ZIOCC/Zio-Qwiic-Ultrasonic-Distance-Sensor/STM8 Gateway Firmware/STM8L15x_StdPeriph_Driver/inc/stm8l15x_rtc.h

/**
  ******************************************************************************
  * @file    stm8l15x_rtc.h
  * @author  MCD Application Team
  * @version V1.5.0
  * @date    13-May-2011
  * @brief   This file contains all the functions prototypes for the RTC 
  *          firmware library.
  ******************************************************************************
  * @attention
  *
  * THE PRESENT FIRMWARE WHICH IS FOR GUIDANCE ONLY AIMS AT PROVIDING CUSTOMERS
  * WITH CODING INFORMATION REGARDING THEIR PRODUCTS IN ORDER FOR THEM TO SAVE
  * TIME. AS A RESULT, STMICROELECTRONICS SHALL NOT BE HELD LIABLE FOR ANY
  * DIRECT, INDIRECT OR CONSEQUENTIAL DAMAGES WITH RESPECT TO ANY CLAIMS ARISING
  * FROM THE CONTENT OF SUCH FIRMWARE AND/OR THE USE MADE BY CUSTOMERS OF THE
  * CODING INFORMATION CONTAINED HEREIN IN CONNECTION WITH THEIR PRODUCTS.
  *
  * <h2><center>&copy; COPYRIGHT 2011 STMicroelectronics</center></h2>
  ******************************************************************************  
  */
/* Define to prevent recursive inclusion -------------------------------------*/
#ifndef __STM8L15x_RTC_H
#define __STM8L15x_RTC_H

/* Includes ------------------------------------------------------------------*/
#include "stm8l15x.h"

/** @addtogroup STM8L15x_StdPeriph_Driver
  * @{
  */

/** @addtogroup RTC
  * @{
  */ 
  
/* Exported types ------------------------------------------------------------*/
/** @defgroup RTC_Exported_Types
  * @{
  */

/** @defgroup RTC_Weekdays
  * @{
  */ 
typedef enum
{
  RTC_Weekday_Monday      =  ((uint8_t)0x01), /*!< WeekDay is Monday */
  RTC_Weekday_Tuesday     =  ((uint8_t)0x02), /*!< WeekDay is Tuesday */
  RTC_Weekday_Wednesday   =  ((uint8_t)0x03), /*!< WeekDay is Wednesday */
  RTC_Weekday_Thursday    =  ((uint8_t)0x04), /*!< WeekDay is Thursday */
  RTC_Weekday_Friday      =  ((uint8_t)0x05), /*!< WeekDay is Friday */
  RTC_Weekday_Saturday    =  ((uint8_t)0x06), /*!< WeekDay is Saturday */
  RTC_Weekday_Sunday      =  ((uint8_t)0x07)  /*!< WeekDay is Sunday */
}
RTC_Weekday_TypeDef;

/**
  * @}
  */
  
/** @defgroup RTC_Months
  * @{
  */ 
typedef enum
{
  RTC_Month_January   =  ((uint8_t)0x01), /*!< Month is January */
  RTC_Month_February  =  ((uint8_t)0x02), /*!< Month is February */
  RTC_Month_March     =  ((uint8_t)0x03), /*!< Month is March */
  RTC_Month_April     =  ((uint8_t)0x04), /*!< Month is April */
  RTC_Month_May       =  ((uint8_t)0x05), /*!< Month is May */
  RTC_Month_June      =  ((uint8_t)0x06), /*!< Month is June */
  RTC_Month_July      =  ((uint8_t)0x07), /*!< Month is July */
  RTC_Month_August    =  ((uint8_t)0x08), /*!< Month is August */
  RTC_Month_September =  ((uint8_t)0x09), /*!< Month is September */
  RTC_Month_October   =  ((uint8_t)0x10), /*!< Month is October */
  RTC_Month_November  =  ((uint8_t)0x11), /*!< Month is November */
  RTC_Month_December  =  ((uint8_t)0x12)  /*!< Month is December */
}
RTC_Month_TypeDef;

/**
  * @}
  */
  
/** @defgroup RTC_Hour_Format
  * @{
  */ 
typedef enum
{
  RTC_HourFormat_24  = ((uint8_t)0x00), /*!< Hour Format is 24H */
  RTC_HourFormat_12  = ((uint8_t)0x40)  /*!< Hour Format is 12H (using AM/PM) */
}
RTC_HourFormat_TypeDef;

/**
  * @}
  */
  
/** @defgroup RTC_Time
  * @{
  */ 
typedef enum
{
  RTC_H12_AM     = ((uint8_t)0x00), /*!< AM/PM notation is AM or 24 hour format */
  RTC_H12_PM     = ((uint8_t)0x40)  /*!< AM/PM notation is PM  */
}
RTC_H12_TypeDef;

/**
  * @}
  */
  
/** @defgroup RTC_Alarm_WeekDay_Selection
  * @{
  */ 
typedef enum
{
  RTC_AlarmDateWeekDaySel_Date     = ((uint8_t)0x00), /*!< Date/WeekDay selection is Date */
  RTC_AlarmDateWeekDaySel_WeekDay  = ((uint8_t)0x40)  /*!< Date/WeekDay selection is WeekDay */
}
RTC_AlarmDateWeekDaySel_TypeDef;

/**
  * @}
  */
  
/** @defgroup RTC_Alarm_Mask
  * @{
  */ 
typedef enum
{
  RTC_AlarmMask_None         =  ((uint8_t)0x00), /*!< Alarm Masks disabled */
  RTC_AlarmMask_Seconds      =  ((uint8_t)0x80), /*!< Alarm Seconds Mask */
  RTC_AlarmMask_Minutes      =  ((uint8_t)0x40), /*!< Alarm Minutes Mask */
  RTC_AlarmMask_Hours        =  ((uint8_t)0x20), /*!< Alarm Hours Mask */
  RTC_AlarmMask_DateWeekDay  =  ((uint8_t)0x10), /*!< Alarm Date/WeekDay Mask */
  RTC_AlarmMask_All          =  ((uint8_t)0xF0)  /*!< Alarm All Mask are enabled */
}
RTC_AlarmMask_TypeDef;

/**
  * @}
  */
  
/** @defgroup RTC_Sub_Second_Alarm_Mask
  * @{
  */ 
typedef enum
{
  RTC_AlarmSubSecondMask_All      =  ((uint8_t)0x00), /*!< All Alarm SS fields are masked. There is no comparison on sub seconds for Alarm */
  RTC_AlarmSubSecondMask_None     =  ((uint8_t)0x0F), /*!< SS[14:0] are compared and must match to activate alarm. */
  RTC_AlarmSubSecondMask_SS14_1   =  ((uint8_t)0x01), /*!< SS[14:1] are not used in Alarm comparison. Only SS[0] is compared. */
  RTC_AlarmSubSecondMask_SS14_2   =  ((uint8_t)0x02), /*!< SS[14:2] are not used in Alarm comparison. Only SS[1:0] are compared */
  RTC_AlarmSubSecondMask_SS14_3   =  ((uint8_t)0x03), /*!< SS[14:3] are not used in Alarm comparison. Only SS[1:0] are compared */
  RTC_AlarmSubSecondMask_SS14_4   =  ((uint8_t)0x04), /*!< SS[14:4] are not used in Alarm comparison. Only SS[1:0] are compared */
  RTC_AlarmSubSecondMask_SS14_5   =  ((uint8_t)0x05), /*!< SS[14:5] are not used in Alarm comparison. Only SS[1:0] are compared */
  RTC_AlarmSubSecondMask_SS14_6   =  ((uint8_t)0x06), /*!< SS[14:6] are not used in Alarm comparison. Only SS[1:0] are compared */
  RTC_AlarmSubSecondMask_SS14_7   =  ((uint8_t)0x07), /*!< SS[14:7] are not used in Alarm comparison. Only SS[1:0] are compared */
  RTC_AlarmSubSecondMask_SS14_8   =  ((uint8_t)0x08), /*!< SS[14:8] are not used in Alarm comparison. Only SS[1:0] are compared */
  RTC_AlarmSubSecondMask_SS14_9   =  ((uint8_t)0x09), /*!< SS[14:9] are not used in Alarm comparison. Only SS[1:0] are compared */
  RTC_AlarmSubSecondMask_SS14_10  =  ((uint8_t)0x0A), /*!< SS[14:10] are not used in Alarm comparison. Only SS[1:0] are compared */
  RTC_AlarmSubSecondMask_SS14_11  =  ((uint8_t)0x0B), /*!< SS[14:11] are not used in Alarm comparison. Only SS[1:0] are compared */
  RTC_AlarmSubSecondMask_SS14_12  =  ((uint8_t)0x0C), /*!< SS[14:12] are not used in Alarm comparison. Only SS[1:0] are compared */
  RTC_AlarmSubSecondMask_SS14_13  =  ((uint8_t)0x0D), /*!< SS[14:13] are not used in Alarm comparison. Only SS[1:0] are compared */
  RTC_AlarmSubSecondMask_SS14     =  ((uint8_t)0x0E) /*!< SS[14] is not used in Alarm comparison. Only SS[13:0] are compared */
}
RTC_AlarmSubSecondMask_TypeDef;

/**
  * @}
  */
  
/** @defgroup RTC_Wakeup_Clock
  * @{
  */ 
typedef enum
{
  RTC_WakeUpClock_RTCCLK_Div16    = ((uint8_t)0x00), /*!< (RTC clock) div 16*/
  RTC_WakeUpClock_RTCCLK_Div8     = ((uint8_t)0x01), /*!< (RTC clock) div 8*/
  RTC_WakeUpClock_RTCCLK_Div4     = ((uint8_t)0x02), /*!< (RTC clock) div 4*/
  RTC_WakeUpClock_RTCCLK_Div2     = ((uint8_t)0x03), /*!< (RTC clock) div 2*/
  RTC_WakeUpClock_CK_SPRE_16bits  = ((uint8_t)0x04), /*!< CK SPRE with a counter from 0x0000 to 0xFFFF */
  RTC_WakeUpClock_CK_SPRE_17bits  = ((uint8_t)0x06)  /*!< CK SPRE with a counter from 0x10000 to 0x1FFFF */
}
RTC_WakeUpClock_TypeDef;

/**
  * @}
  */
  
/** @defgroup RTC_Output_Selection
  * @{
  */ 
typedef enum
{
  RTC_Output_Disable = ((uint8_t)0x00), /*!< RTC Alternate function Output is disabled  */
  RTC_Output_Alarm   = ((uint8_t)0x20), /*!< RTC Alternate function Output is the Alarm A event*/
  RTC_Output_WakeUp  = ((uint8_t)0x60)  /*!< RTC Alternate function Output is the WakeUp event */
}
RTC_Output_TypeDef;

/**
  * @}
  */
  
/** @defgroup RTC_Output_Polarity
  * @{
  */ 
typedef enum
{
  RTC_OutputPolarity_High  = ((uint8_t)0x00), /*!< RTC Alternate function Output Polarity is High  */
  RTC_OutputPolarity_Low   = ((uint8_t)0x10)  /*!< RTC Alternate function Output Polarity is Low  */
}
RTC_OutputPolarity_TypeDef;

/**
  * @}
  */
  
/** @defgroup RTC_Calibration_Output
  * @{
  */ 
typedef enum
{
  RTC_CalibOutput_512Hz  = ((uint8_t)0x00), /*!< RTC Calibration Output is 512Hz */
  RTC_CalibOutput_1Hz    = ((uint8_t)0x80)  /*!< RTC Calibration Output is 1Hz */
}
RTC_CalibOutput_TypeDef;

/**
  * @}
  */
  
/** @defgroup RTC_DayLight_Saving
  * @{
  */ 
typedef enum
{
  RTC_DayLightSaving_SUB1H  = ((uint8_t)0x02), /*!< Substract 1 hour to the current Time (Winter Time Adjustment) */
  RTC_DayLightSaving_ADD1H  = ((uint8_t)0x01)  /*!< Add 1 hour to the current Time (Summer Time Adjustment) */
}
RTC_DayLightSaving_TypeDef;

/**
  * @}
  */
  
/** @defgroup RTC_Store_Operation
  * @{
  */ 
typedef enum
{
  RTC_StoreOperation_Set   = ((uint8_t)0x04), /*!< Store Operation Set */
  RTC_StoreOperation_Reset = ((uint8_t)0x00)  /*!< Store Operation Reset */
}
RTC_StoreOperation_TypeDef;

/**
  * @}
  */
  
/** @defgroup RTC_Input_Parameter_Format
  * @{
  */ 
typedef enum
{
  RTC_Format_BIN  = ((uint8_t)0x00), /*!< Binary Format is used  */
  RTC_Format_BCD  = ((uint8_t)0x01)  /*!< BCD Format is used  */
}
RTC_Format_TypeDef;

/**
  * @}
  */
  
/** @defgroup RTC_Flags
  * @{
  */ 
typedef enum
{
  RTC_FLAG_TAMP3F  = ((uint16_t)0x0080), /*!< TAMPER3 detection  Flag. If set, tamper detection event is detected on tamper input 3 */
  RTC_FLAG_TAMP2F  = ((uint16_t)0x0040), /*!< TAMPER2 detection  Flag. If set, tamper detection event is detected on tamper input 2 */
  RTC_FLAG_TAMP1F  = ((uint16_t)0x0020), /*!< TAMPER1 detection  Flag. If set, tamper detection event is detected on tamper input 1 */

  RTC_FLAG_WUTF    = ((uint16_t)0x0004), /*!< Wake up Timer Flag. If set, the Wake Up down counter reaches 0 */
  RTC_FLAG_ALRAF   = ((uint16_t)0x0001), /*!< Alarm A Flag. If set, the Time/Date registers matches Alarm A registers */

  RTC_FLAG_INITF   = ((uint16_t)0x4000), /*!< Initialisation Flag. If set,Calender registers has been initialized  */
  RTC_FLAG_RSF     = ((uint16_t)0x2000), /*!< Registers Synchronization Flag. If set,Calender registers synchronized  */
  RTC_FLAG_INITS   = ((uint16_t)0x1000), /*!< Initialisation Status Flag. If set,Calender  update is allowed  */

  RTC_FLAG_SHPF    = ((uint16_t)0x0800), /*!< Shift operation pending Flag. This flag is set by hardware as soon as a shift operation is
                                              initiated by a write to the RTC_SHIFTRL. It is cleared by hardware as soon as the corresponding
                                              shift operation has completed.  */

  RTC_FLAG_WUTWF   = ((uint16_t)0x0400), /*!< Wake up Timer write Flag. If set, Wake up Timer update is allowed */
  RTC_FLAG_RECALPF = ((uint16_t)0x0200), /*!<   Recalibration pending Flag, The status flag RECALPF is automatically set to ‘1’ when software
                                                writes to the register RTC_CALRL, indicating that the RTC_CALRx registers are blocked.
                                                When the new calibration settings are taken into account, this Flag returns by hardware to ‘0’. */
  RTC_FLAG_ALRAWF  = ((uint16_t)0x0100)  /*!< Alarm  A write Flag. If set, Alarm A update is allowed   */
}
RTC_Flag_TypeDef;

/**
  * @}
  */
  
/** @defgroup RTC_Interrupts
  * @{
  */ 
typedef enum
{
  RTC_IT_WUT  = ((uint16_t)0x0040),  /*!< Wake up Timer Interrupt */
  RTC_IT_ALRA = ((uint16_t)0x0010),  /*!< Alarm A Interrupt */
  RTC_IT_TAMP = ((uint16_t)0x0F01)   /*!< Tamper Interrupt */
}
RTC_IT_TypeDef;

/**
  * @}
  */

/** @defgroup RTC_Tamper_Level
  * @{
  */ 
typedef enum
{
  RTC_TamperLevel_Low    = ((uint8_t)0x00), /*!< Tamper staying low triggers a tamper detection event. */
  RTC_TamperLevel_High   = ((uint8_t)0x54)  /*!< Tamper staying high triggers a tamper detection event. */
}
RTC_TamperLevel_TypeDef;

/**
  * @}
  */
  
/** @defgroup RTC_Tamper_State
  * @{
  */ 
typedef enum
{
  RTC_TamperState_Disable  = ((uint8_t)0x00), /*!< Tamper State is Disable */
  RTC_TamperState_Enable   = ((uint8_t)0x01)  /*!< Tamper State is Enable  */
}
RTC_TamperState_TypeDef;

/**
  * @}
  */
  
/** @defgroup RTC_Tamper_definition
  * @{
  */ 
typedef enum
{
  RTC_Tamper_1 = ((uint8_t)0x02),  /*!< Tamper 1 selection */
  RTC_Tamper_2 = ((uint8_t)0x08),  /*!< Tamper 2 selection */
  RTC_Tamper_3 = ((uint8_t)0x20)   /*!< Tamper 3 selection */
}
RTC_Tamper_TypeDef;

/**
  * @}
  */
  
/** @defgroup RTC_Tamper_Precharge_Duration
  * @{
  */ 
typedef enum
{
  RTC_TamperPrechargeDuration_None    = ((uint8_t)0x80),  /*!< Tamper pins are not precharged before sampling */
  RTC_TamperPrechargeDuration_1RTCCLK = ((uint8_t)0x00),  /*!< Tamper pins are precharged before sampling during 1 RTCCLK cycle  */
  RTC_TamperPrechargeDuration_2RTCCLK = ((uint8_t)0x20),  /*!< Tamper pins are precharged before sampling during 2 RTCCLK cycles */
  RTC_TamperPrechargeDuration_4RTCCLK = ((uint8_t)0x40),  /*!< Tamper pins are precharged before sampling during 4 RTCCLK cycles */
  RTC_TamperPrechargeDuration_8RTCCLK = ((uint8_t)0x60)   /*!< Tamper pins are precharged before sampling during 8 RTCCLK cycles */
}
RTC_TamperPrechargeDuration_TypeDef;

/**
  * @}
  */
  
/** @defgroup RTC_Tamper_Filter
  * @{
  */ 
typedef enum
{
  RTC_TamperFilter_1Sample    = ((uint8_t)0x00), /*!< Tamper is activated after 1 sample at the active level */
  RTC_TamperFilter_2Sample    = ((uint8_t)0x08), /*!< Tamper is activated after 2 consecutive samples at the active level. */
  RTC_TamperFilter_4Sample    = ((uint8_t)0x10), /*!< Tamper is activated after 4 consecutive samples at the active level. */
  RTC_TamperFilter_8Sample    = ((uint8_t)0x18)  /*!< Tamper is activated after 8 consecutive samples at the active level. */
}
RTC_TamperFilter_TypeDef;

/**
  * @}
  */
  
/** @defgroup RTC_Tamper_Sampling_Frequency
  * @{
  */ 
typedef enum
{
  RTC_TamperSamplingFreq_RTCCLK_Div32768  = ((uint8_t)0x00), /*!< Tamper inputs are sampled with a frequency =  RTCCLK / 32768 */
  RTC_TamperSamplingFreq_RTCCLK_Div16384  = ((uint8_t)0x01), /*!< Tamper inputs are sampled with a frequency =  RTCCLK / 16384 */
  RTC_TamperSamplingFreq_RTCCLK_Div8192   = ((uint8_t)0x02), /*!< Tamper inputs are sampled with a frequency =  RTCCLK / 8192  */
  RTC_TamperSamplingFreq_RTCCLK_Div4096   = ((uint8_t)0x03), /*!< Tamper inputs are sampled with a frequency =  RTCCLK / 4096  */
  RTC_TamperSamplingFreq_RTCCLK_Div2048   = ((uint8_t)0x04), /*!< Tamper inputs are sampled with a frequency =  RTCCLK / 2048  */
  RTC_TamperSamplingFreq_RTCCLK_Div1024   = ((uint8_t)0x05), /*!< Tamper inputs are sampled with a frequency =  RTCCLK / 1024  */
  RTC_TamperSamplingFreq_RTCCLK_Div512    = ((uint8_t)0x06), /*!< Tamper inputs are sampled with a frequency =  RTCCLK / 512   */
  RTC_TamperSamplingFreq_RTCCLK_Div256    = ((uint8_t)0x07)  /*!< Tamper inputs are sampled with a frequency =  RTCCLK / 256   */
}
RTC_TamperSamplingFreq_TypeDef;

/**
  * @}
  */
  
/** @defgroup RTC_Shift_Add_1s
  * @{
  */ 
typedef enum
{
  RTC_ShiftAdd1S_Set    = ((uint8_t)0x80), /*!< Add 1 Second */
  RTC_ShiftAdd1S_Reset  = ((uint8_t)0x00)  /*!< Do not Add 1 Second */
}
RTC_ShiftAdd1S_TypeDef;

/**
  * @}
  */
  
/** @defgroup RTC_Smooth_Calibration_Period
  * @{
  */ 
typedef enum
{
  RTC_SmoothCalibPeriod_32sec  = ((uint8_t)0x00), /*!<  if RTCCLK = 32768 Hz, Smooth calibration period is 32s,  else 2exp20 RTCCLK seconds */
  RTC_SmoothCalibPeriod_16sec  = ((uint8_t)0x20), /*!<  if RTCCLK = 32768 Hz, Smooth calibration period is 16s, else 2exp19 RTCCLK seconds */
  RTC_SmoothCalibPeriod_8sec   = ((uint8_t)0x40)  /*!<  if RTCCLK = 32768 Hz, Smooth calibration period is 8s, else 2exp18 RTCCLK seconds */
}
RTC_SmoothCalibPeriod_TypeDef;

/**
  * @}
  */
  
/** @defgroup RTC_Smooth_Calibration_Pulses
  * @{
  */ 
typedef enum
{
  RTC_SmoothCalibPlusPulses_Set    = ((uint8_t)0x80), /*!<  The number of RTCCLK pulses added during a X -second window =  Y  - CALM[8:0].  
                                                             with Y = 512, 256, 128 when X = 32, 16, 8 */
  RTC_SmoothCalibPlusPulses_Reset  = ((uint8_t)0x00)  /*!<  The number of RTCCLK pulses substituted during a 32-second window =  CALM[8:0]. */

}
RTC_SmoothCalibPlusPulses_TypeDef;

/**
  * @}
  */

/**
  * @brief RTC Init structure definition
  */

typedef struct
{

  RTC_HourFormat_TypeDef RTC_HourFormat; /*!< RTC Hour Format */

  uint8_t RTC_AsynchPrediv;   /*!< RTC Asynchronous Predivider.
                                   This parameter can be any value from 
                                   0x00 to 0x7F.*/

  uint16_t RTC_SynchPrediv;   /*!< RTC Synchronous Predivider.
                                   This parameter can be any value from 
                                   0x0000 to 0x7FFF.*/
}
RTC_InitTypeDef;
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
